wirehead/6502-hack-day-build/6502 hack day project 1.sch

## KiCad design 6502 hack day project 1.sch (2020-05-24, an earlier design)

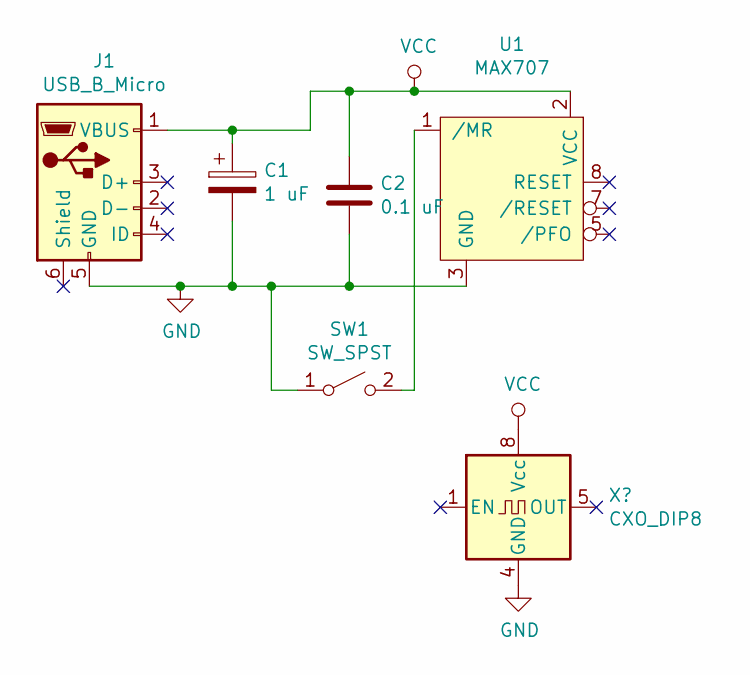
[picture p1: schematic 6502 hack day project 1.sch]

Parts:
C1: 1 uF
C2: 0.1 uF
J1: USB_B_Micro
SW1: SW_SPST
U1: MAX707

Connections:
GND: C1.2, C2.2, J1.5 (GND), SW1.1 (A), U1.3 (GND)
unnamed: SW1.2 (B), U1.1 (/MR)
VCC: C1.1, C2.1, J1.1 (VBUS), U1.2 (VCC)
